Xi-Jian-Lee/He-thong-giam-sat-moi-truong-va-nong-do-CO-tu-xa/Bitmap.h

#ifndef _BITMAP_H__
#define _BITMAP_H__
// hiển thị lên màn hình 
// const uint8_t  wifi_Strong_bm đẩy biểu tưởng wifi mạnh lên màn hình
const uint8_t  wifi_Strong_bmp[] PROGMEM = {
B00000000, B00000000, B00000000, B00000000,  
B00000000, B00000000, B00000000, B00000000,  
B00000000, B00000000, B00000000, B00000000,  
B00000000, B00000111, B11100000, B00000000,  
B00000000, B01111111, B11111110, B00000000,  
B00000011, B11111111, B11111111, B11000000,  
B00000111, B11111111, B11111111, B11100000,  
B00011111, B11111100, B00111111, B11111000,  
B00111111, B11000000, B00000011, B11111100,  
B01111110, B00000011, B11000000, B01111110,  
B11111100, B00111111, B11111100, B00111111,  
B11110000, B11111111, B11111111, B00001111,  
B11100001, B11111111, B11111111, B10000111,  
B00000111, B11111111, B11111111, B11100000,  
B00001111, B11100000, B00000111, B11110000,  
B00001111, B10000000, B00000001, B11110000,  
B00001111, B00001111, B11110000, B11110000,  
B00000000, B00111111, B11111100, B00000000,  
B00000000, B01111111, B11111110, B00000000,  
B00000000, B11111111, B11111111, B00000000,  
B00000000, B01111000, B00011110, B00000000,  
B00000000, B01100000, B00000110, B00000000,  
B00000000, B00000011, B11000000, B00000000,  
B00000000, B00000111, B11100000, B00000000,  
B00000000, B00001111, B11110000, B00000000,  
B00000000, B00001111, B11110000, B00000000,  
B00000000, B00000111, B11100000, B00000000,  
B00000000, B00000011, B11000000, B00000000,  
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
B00000000, B00000000, B00000000, B00000000,  
B00000000, B00000000, B00000000, B00000000,  
B00000000, B00000000, B00000000, B00000000,  
B00000000, B00000000, B00000000, B00000000,  
B00000000, B00000000, B00000000, B00000000,  
B00000000, B00000000, B00000000, B00000000,  
B00000000, B00000000, B00000000, B00000000,  
B00000000, B00000011, B11000000, B00000000,  
B00000000, B00000111, B11100000, B00000000,  
B00000000, B00001111, B11110000, B00000000,  
B00000000, B00001111, B11110000, B00000000,  
B00000000, B00000111, B11100000, B00000000,  
B00000000, B00000011, B11000000, B00000000,  
B00000000, B00000000, B00000000, B00000000,  
B00000000, B00000000, B00000000, B00000000,  
B00000000, B00000000, B00000000, B00000000,  
B00000000, B00000000, B00000000, B00000000, 
};

#endif
